franblas/ArmRobot/STM32/main.c

/*	****** Written by François Blas
	****** Last Modification: 25/05/13 	
	****** Tested on STM32F100RB */

#include "automatismeAX12.h"

int main()
{
/* Fonction principale */
moveARM(USART_1);

/* Fonction prinpale (demonstration) */
//moveARMDemo(USART_1);
}
